eduardocasino/kim-1/3dmodels/C_Axial_L17.0mm_D6.5mm_P38.10mm_Horizontal.step

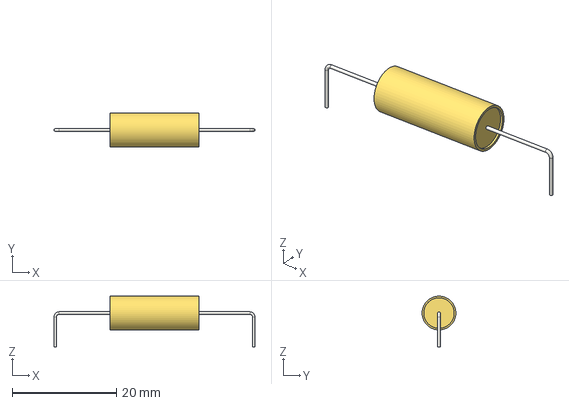
[picture p18: CAD file, 2023-03-21]
3dmodels/C_Axial_L17.0mm_D6.5mm_P38.10mm_Horizontal.step
38.6 x 6.49 x 9.75 mm
190bb9c4-b13a-11ed-bc6f-67ea0efcc404_part
190bb9c5-b13a-11ed-bc6f-67ea0efcc404_part
