eduardocasino/kim-1/3dmodels/C_Disc_D9.0mm_W2.5mm_P13.00mm.step

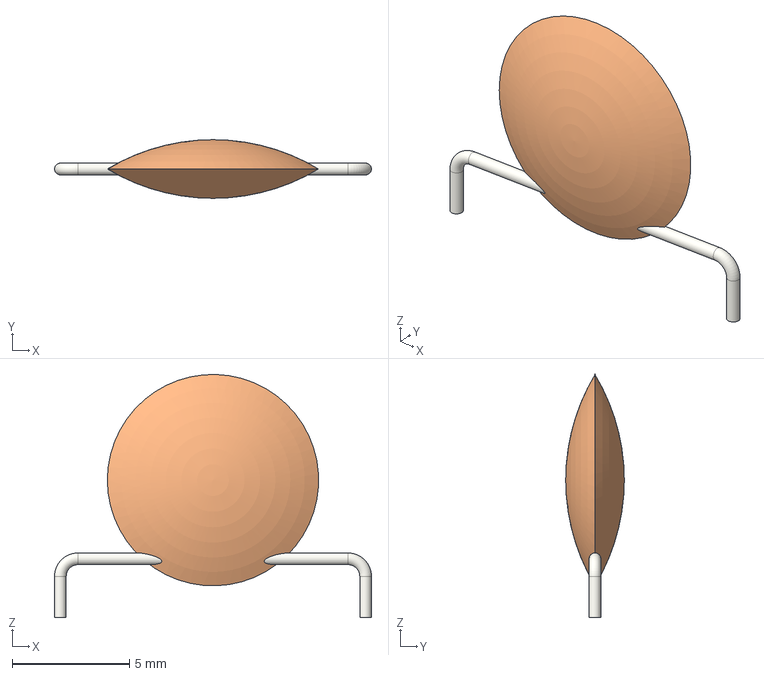
[picture p19: CAD file, 2023-03-21]
3dmodels/C_Disc_D9.0mm_W2.5mm_P13.00mm.step
13.5 x 2.50 x 10.3 mm
190bb9d0-b13a-11ed-bc6f-67ea0efcc404_part
190bb9d1-b13a-11ed-bc6f-67ea0efcc404_part
