eduardocasino/kim-1/3dmodels/C_Axial_L12.0mm_D4.5mm_P22.86mm_Horizontal.step

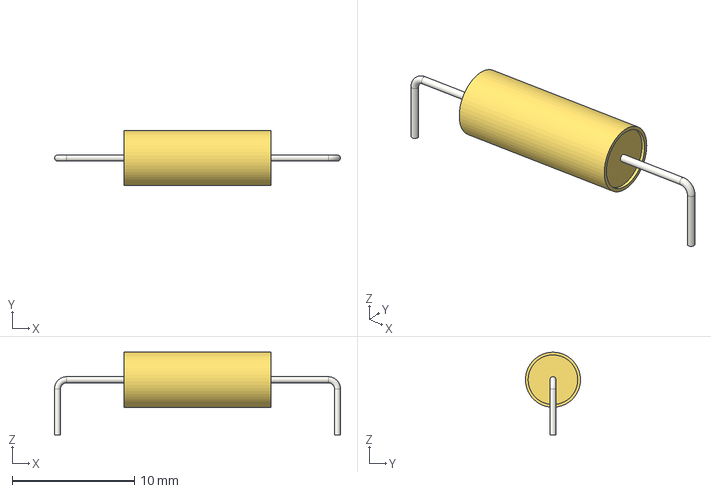
[picture p20: CAD file, 2023-03-21]
3dmodels/C_Axial_L12.0mm_D4.5mm_P22.86mm_Horizontal.step
23.4 x 4.50 x 6.75 mm
0d44160d-c6fe-11ed-94c9-bdfa26a9df0a_part
0d44160e-c6fe-11ed-94c9-bdfa26a9df0a_part
