eduardocasino/kim-1/3dmodels/res-1_4w-150R-18_0mm-Resistor-1_4w-220ohm.step

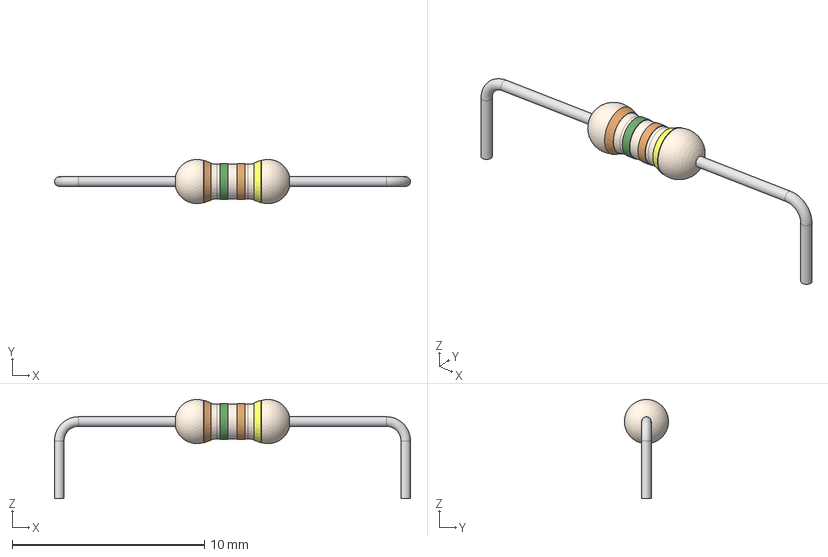
[picture p21: CAD file, 2023-03-21]
3dmodels/res-1_4w-150R-18_0mm-Resistor-1_4w-220ohm.step
18.5 x 2.29 x 5.14 mm
Resistor-body
Ring-1
Ring-2
Ring-3
Ring-4
pins
