eduardocasino/kim-1/kim-1.kicad_sch

## KiCad design kim-1.kicad_sch (2023-03-21)

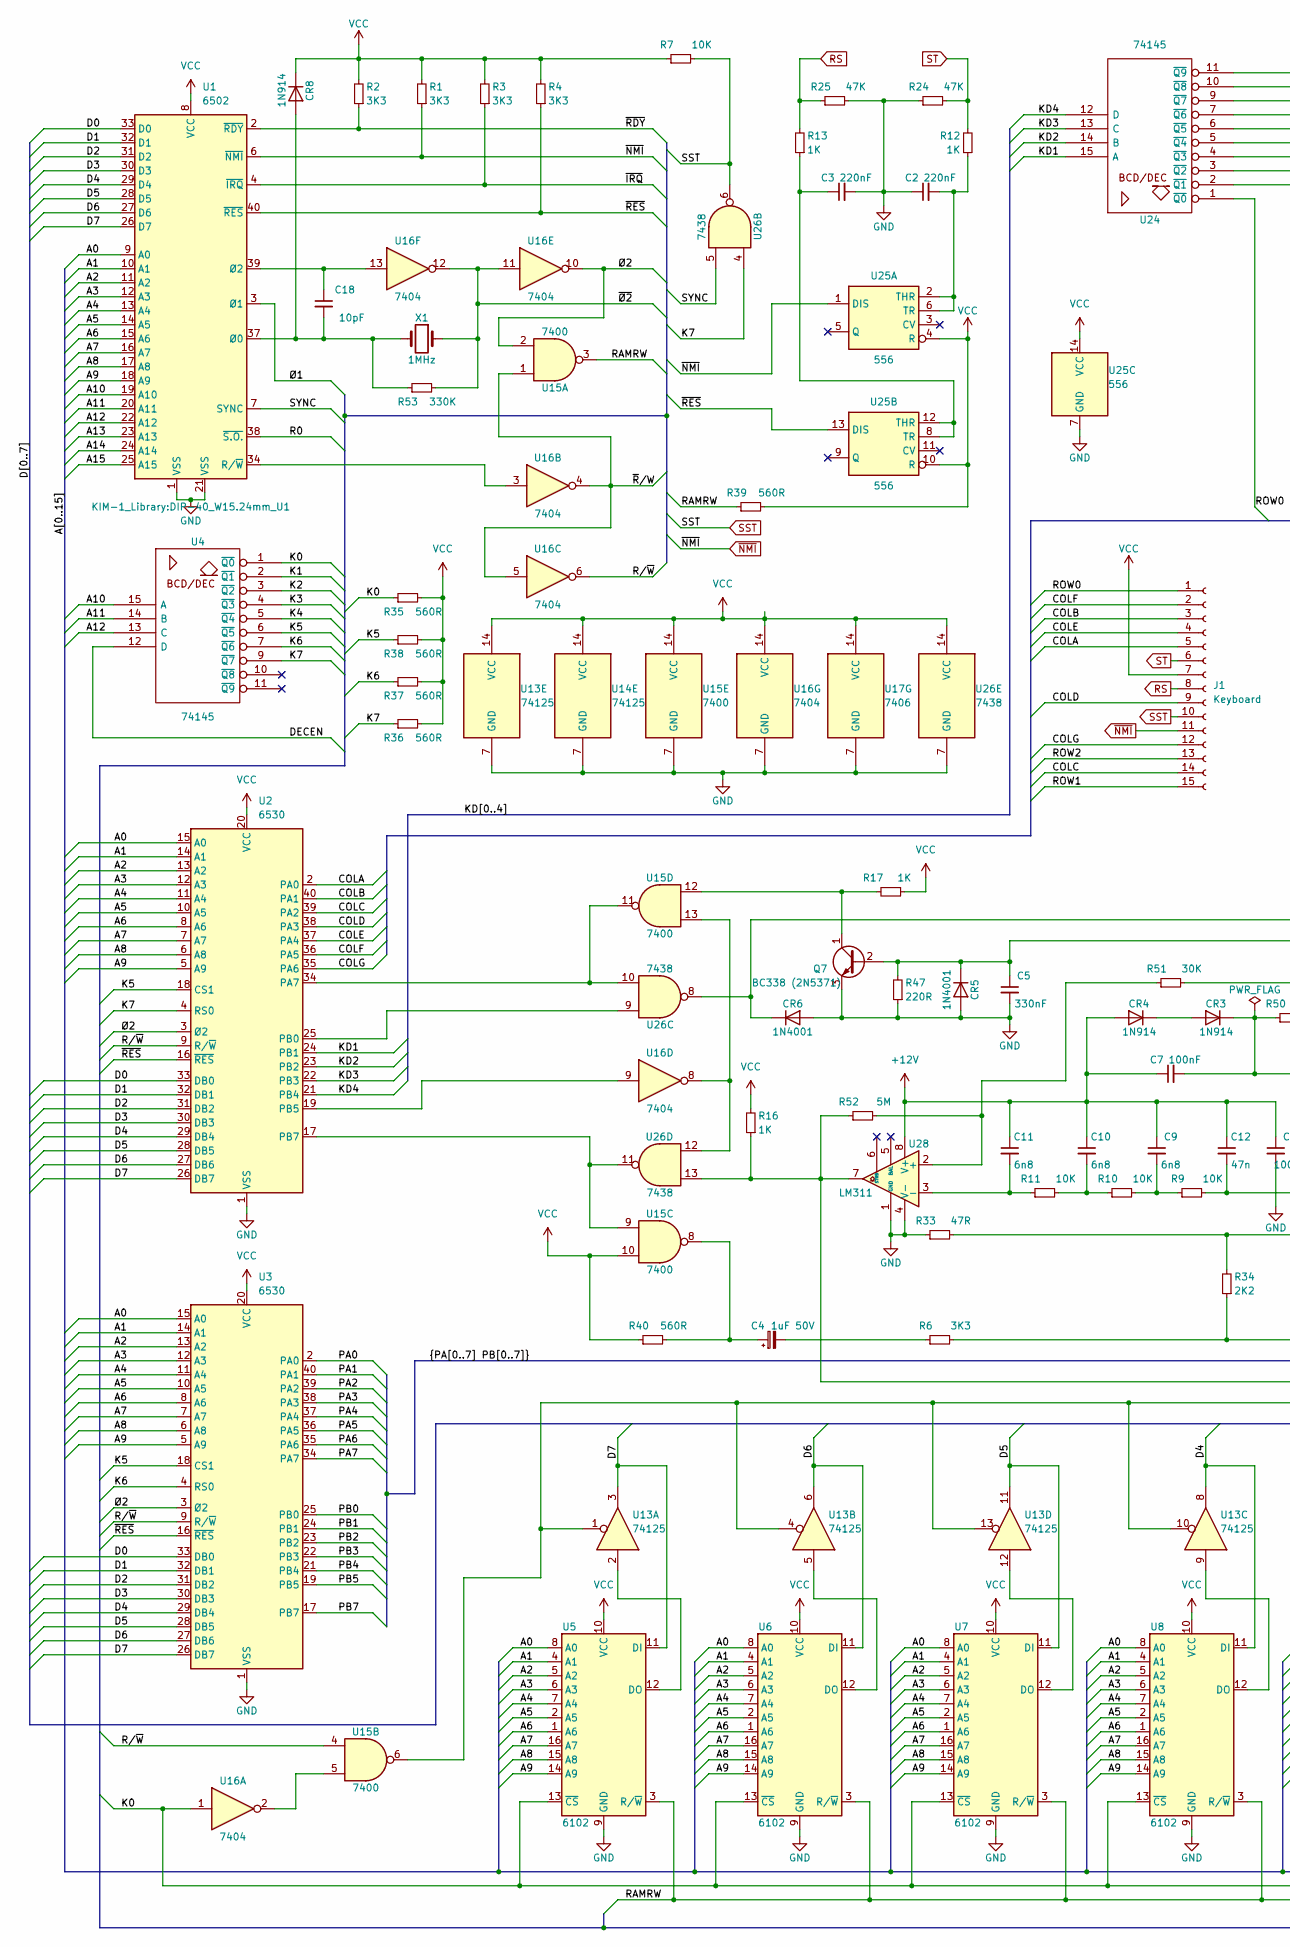
[picture p23: schematic kim-1.kicad_sch, part in row 1, column 1]

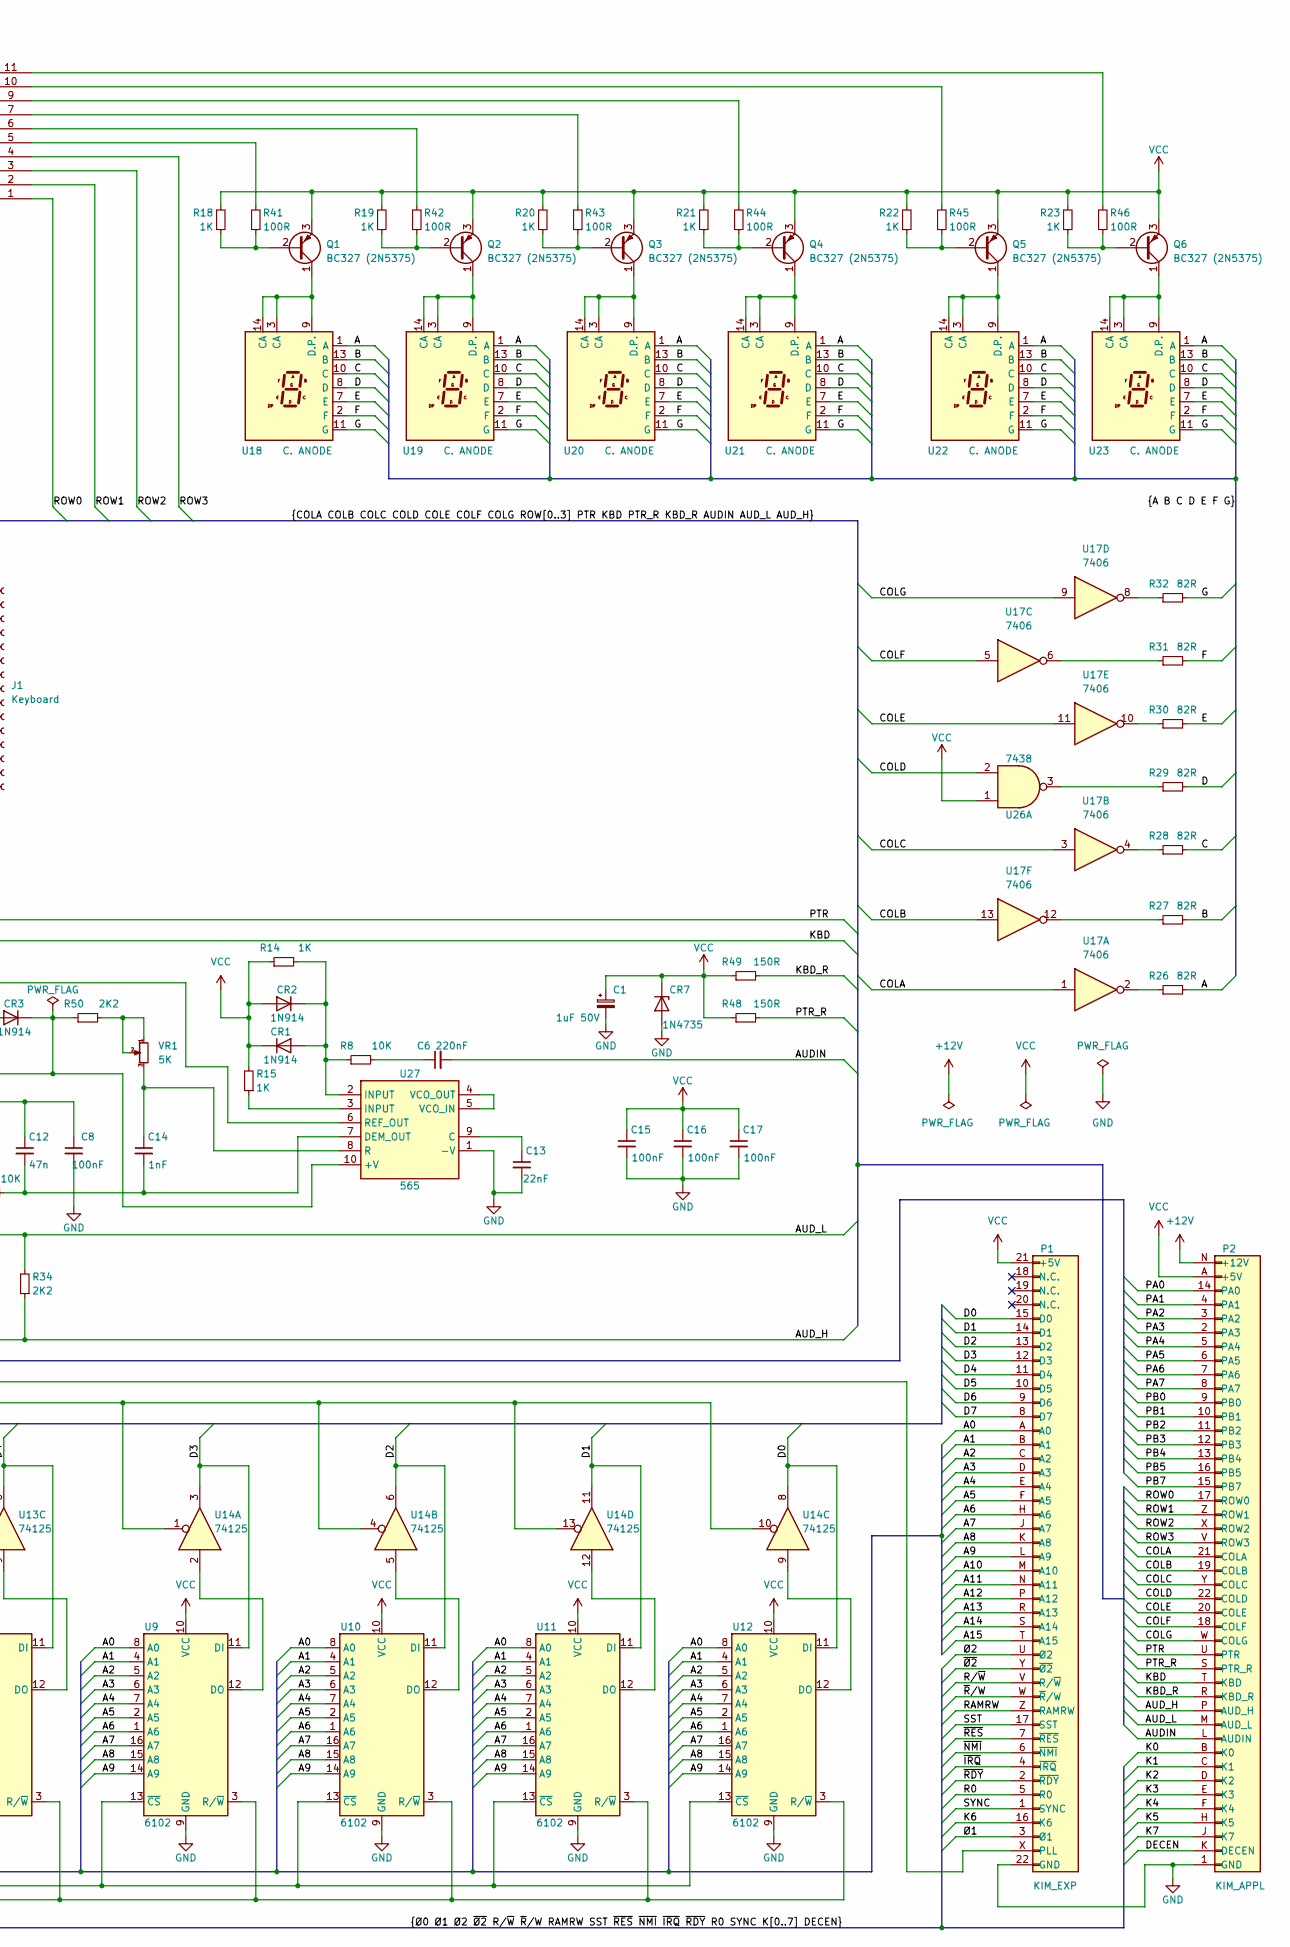
[picture p24: schematic kim-1.kicad_sch, part in row 1, column 2]

Parts:
C1, C4: 1uF 50V; CP_Axial_L11.0mm_D5.0mm_P22.86mm_Horizontal
C2, C3, C6: 220nF; C_Axial_L17.0mm_D6.5mm_P38.10mm_Horizontal
C5: 330nF; C_Axial_L17.0mm_D6.5mm_P43.18mm_Horizontal
C7, C8, C15, C16, C17: 100nF; C_Axial_L17.0mm_D6.5mm_P35.56mm_Horizontal
C9, C10, C11: 6n8; C_Axial_L12.0mm_D4.5mm_P22.86mm_Horizontal
C12: 47n; C_Axial_L12.0mm_D5.0mm_P30.48mm_Horizontal
C13: 22nF; C_Axial_L12.0mm_D5.0mm_P30.48mm_Horizontal
C14: 1nF; C_Axial_L12.0mm_D4.5mm_P22.86mm_Horizontal
C18: 10pF; C_Disc_D9.0mm_W2.5mm_P13.00mm
CR1, CR2, CR3, CR4, CR8: 1N914; D_DO-35_SOD27_P12.70mm_Horizontal
CR5, CR6: 1N4001; D_DO-41_SOD81_P12.70mm_Horizontal
CR7: 1N4735; D_DO-41_SOD81_P12.30mm_Horizontal
J1: Keyboard; PinSocket_1x15_P2.54mm_Vertical
P1: KIM_EXP; KIM_CONN
P2: KIM_APPL; KIM_CONN
Q1, Q2, Q3, Q4, Q5, Q6: BC327 (2N5375); TO-92
Q7: BC338 (2N5371); TO-92
R1, R2, R3: 3K3; R_Axial_DIN0207_3K3_L6.3mm_D2.3mm_P13mm_Horizontal
R4, R6: 3K3; R_Axial_DIN0309_3K3_L6.3mm_D2.3mm_P12.70mm_Horizontal
R7, R8, R9, R10, R11: 10K; R_Axial_DIN0309_10K_L6.3mm_D2.3mm_P12.70mm_Horizontal
R12, R13, R14, R15, R16, R17, R18, R19, R20, R21, R22, R23: 1K; R_Axial_DIN0309_1K_L6.3mm_D2.3mm_P12.70mm_Horizontal
R24, R25: 47K; R_Axial_DIN0309_47K_L6.3mm_D2.3mm_P12.70mm_Horizontal
R26, R27, R28, R29, R30, R31, R32: 82R; R_Axial_DIN0309_82R_L6.3mm_D2.3mm_P12.70mm_Horizontal
R33: 47R; R_Axial_DIN0309_47R_L6.3mm_D2.3mm_P12.70mm_Horizontal
R34, R50: 2K2; R_Axial_DIN0309_2K2_L6.3mm_D2.3mm_P12.70mm_Horizontal
R35, R36, R37, R38, R40: 560R; R_Axial_DIN0309_560R_L6.3mm_D2.3mm_P12.70mm_Horizontal
R39: 560R; R_Axial_DIN0309_560R_L6.3mm_D2.3mm_P8.70mm_Horizontal
R41, R42, R43, R44, R45, R46: 100R; R_Axial_DIN0309_100R_L6.3mm_D2.5mm_P12.70mm_Horizontal
R47: 220R; R_Axial_DIN0309_220R_L6.3mm_D2.3mm_P12.70mm_Horizontal
R48, R49: 150R; R_Axial_DIN0309_150R_L9.0mm_D3.2mm_P18.00mm_Horizontal
R51: 30K; R_Axial_DIN0309_30K_L6.3mm_D2.3mm_P12.70mm_Horizontal
R52: 5M; R_Axial_DIN0309_5M_L6.3mm_D2.3mm_P12.70mm_Horizontal
R53: 330K; R_Axial_DIN0207_330K_L6.3mm_D2.3mm_P13mm_Horizontal
U1: 6502; DIP-40_W15.24mm_U1
U2: 6530; DIP-40_W15.24mm_U2
U3: 6530; DIP-40_W15.24mm_U3
U4: 74145; DIP-16_W7.62mm
U5, U6, U7, U8, U9, U10, U11: 6102; DIP-16_W7.62mm_U5-U11
U12: 6102; DIP-16_W7.62mm_U12
U13, U14: 74125; DIP-14_W7.62mm
U15: 7400; DIP-14_W7.62mm
U16: 7404; DIP-14_W7.62mm
U17: 7406; DIP-14_W7.62mm_U17
U18: C. ANODE; MAN72A_U18
U19, U20: C. ANODE; MAN72A_U19-U20
U21: C. ANODE; MAN72A_U21
U22: C. ANODE; MAN72A_U22
U23: C. ANODE; MAN72A_U23
U24: 74145; DIP-16_W7.62mm_U24
U25: 556; DIP-14_W7.62mm
U26: 7438; DIP-14_W7.62mm
U27: 565; DIP-14_W7.62mm
U28: LM311; DIP-8_W7.62mm
VR1: 5K; Piher-PT-15-LV18
X1: 1MHz; Crystal_HC33-U_Horizontal

Connections:
+12V: C7.1, C8.1, C9.1, C10.1, C11.1, C12.1, CR4.2 (A), P2.N (+12V), U28.8 (V+)
A: R26.2, U18.1 (A), U19.1 (A), U20.1 (A), U21.1 (A), U22.1 (A), U23.1 (A)
A0: P1.A (A0), U1.9 (A0), U2.15 (A0), U3.15 (A0), U5.8 (A0), U6.8 (A0), U7.8 (A0), U8.8 (A0), U9.8 (A0), U10.8 (A0), U11.8 (A0), U12.8 (A0)
A1: P1.B (A1), U1.10 (A1), U2.14 (A1), U3.14 (A1), U5.4 (A1), U6.4 (A1), U7.4 (A1), U8.4 (A1), U9.4 (A1), U10.4 (A1), U11.4 (A1), U12.4 (A1)
A2: P1.C (A2), U1.11 (A2), U2.13 (A2), U3.13 (A2), U5.5 (A2), U6.5 (A2), U7.5 (A2), U8.5 (A2), U9.5 (A2), U10.5 (A2), U11.5 (A2), U12.5 (A2)
A3: P1.D (A3), U1.12 (A3), U2.12 (A3), U3.12 (A3), U5.6 (A3), U6.6 (A3), U7.6 (A3), U8.6 (A3), U9.6 (A3), U10.6 (A3), U11.6 (A3), U12.6 (A3)
A4: P1.E (A4), U1.13 (A4), U2.11 (A4), U3.11 (A4), U5.7 (A4), U6.7 (A4), U7.7 (A4), U8.7 (A4), U9.7 (A4), U10.7 (A4), U11.7 (A4), U12.7 (A4)
A5: P1.F (A5), U1.14 (A5), U2.10 (A5), U3.10 (A5), U5.2 (A5), U6.2 (A5), U7.2 (A5), U8.2 (A5), U9.2 (A5), U10.2 (A5), U11.2 (A5), U12.2 (A5)
A6: P1.H (A6), U1.15 (A6), U2.8 (A6), U3.8 (A6), U5.1 (A6), U6.1 (A6), U7.1 (A6), U8.1 (A6), U9.1 (A6), U10.1 (A6), U11.1 (A6), U12.1 (A6)
A7: P1.J (A7), U1.16 (A7), U2.7 (A7), U3.7 (A7), U5.16 (A7), U6.16 (A7), U7.16 (A7), U8.16 (A7), U9.16 (A7), U10.16 (A7), U11.16 (A7), U12.16 (A7)
A8: P1.K (A8), U1.17 (A8), U2.6 (A8), U3.6 (A8), U5.15 (A8), U6.15 (A8), U7.15 (A8), U8.15 (A8), U9.15 (A8), U10.15 (A8), U11.15 (A8), U12.15 (A8)
A9: P1.L (A9), U1.18 (A9), U2.5 (A9), U3.5 (A9), U5.14 (A9), U6.14 (A9), U7.14 (A9), U8.14 (A9), U9.14 (A9), U10.14 (A9), U11.14 (A9), U12.14 (A9)
A10: P1.M (A10), U1.19 (A10), U4.15 (A)
A11: P1.N (A11), U1.20 (A11), U4.14 (B)
A12: P1.P (A12), U1.22 (A12), U4.13 (C)
A13: P1.R (A13), U1.23 (A13)
A14: P1.S (A14), U1.24 (A14)
A15: P1.T (A15), U1.25 (A15)
AUDIN: C6.2, P2.L (AUDIN)
AUD_H: P2.P (AUD_H), R6.2, R34.1
AUD_L: P2.M (AUD_L), R33.2, R34.2
B: R27.2, U18.13 (B), U19.13 (B), U20.13 (B), U21.13 (B), U22.13 (B), U23.13 (B)
C: R28.2, U18.10 (C), U19.10 (C), U20.10 (C), U21.10 (C), U22.10 (C), U23.10 (C)
COLA: J1.5, P2.21 (COLA), U2.2 (PA0), U17.1
COLB: J1.3, P2.19 (COLB), U2.40 (PA1), U17.13
COLC: J1.14, P2.Y (COLC), U2.39 (PA2), U17.3
COLD: J1.9, P2.22 (COLD), U2.38 (PA3), U26.2
COLE: J1.4, P2.20 (COLE), U2.37 (PA4), U17.11
COLF: J1.2, P2.18 (COLF), U2.36 (PA5), U17.5
COLG: J1.12, P2.W (COLG), U2.35 (PA6), U17.9
D: R29.2, U18.8 (D), U19.8 (D), U20.8 (D), U21.8 (D), U22.8 (D), U23.8 (D)
D0: P1.15 (D0), U1.33 (D0), U2.33 (DB0), U3.33 (DB0), U12.11 (DI), U14.8
D1: P1.14 (D1), U1.32 (D1), U2.32 (DB1), U3.32 (DB1), U11.11 (DI), U14.11
D2: P1.13 (D2), U1.31 (D2), U2.31 (DB2), U3.31 (DB2), U10.11 (DI), U14.6
D3: P1.12 (D3), U1.30 (D3), U2.30 (DB3), U3.30 (DB3), U9.11 (DI), U14.3
D4: P1.11 (D4), U1.29 (D4), U2.29 (DB4), U3.29 (DB4), U8.11 (DI), U13.8
D5: P1.10 (D5), U1.28 (D5), U2.28 (DB5), U3.28 (DB5), U7.11 (DI), U13.11
D6: P1.9 (D6), U1.27 (D6), U2.27 (DB6), U3.27 (DB6), U6.11 (DI), U13.6
D7: P1.8 (D7), U1.26 (D7), U2.26 (DB7), U3.26 (DB7), U5.11 (DI), U13.3
DECEN: P2.K (DECEN), U4.12 (D)
E: R30.2, U18.7 (E), U19.7 (E), U20.7 (E), U21.7 (E), U22.7 (E), U23.7 (E)
F: R31.2, U18.2 (F), U19.2 (F), U20.2 (F), U21.2 (F), U22.2 (F), U23.2 (F)
G: R32.2, U18.11 (G), U19.11 (G), U20.11 (G), U21.11 (G), U22.11 (G), U23.11 (G)
GND: C1.2, C2.1, C3.2, C5.2, C8.2, C13.2, C15.2, C16.2, C17.2, CR5.2 (A), CR6.2 (A), CR7.2 (A), P1.22 (GND), P2.1 (GND), Q7.3 (E), R24.1, R25.2, R33.1, R47.1, U1.1 (VSS), U1.21 (VSS), U2.1 (VSS), U3.1 (VSS), U5.9 (GND), U6.9 (GND), U7.9 (GND), U8.9 (GND), U9.9 (GND), U10.9 (GND), U11.9 (GND), U12.9 (GND), U13.7 (GND), U14.7 (GND), U15.7 (GND), U16.7 (GND), U17.7 (GND), U25.7 (GND), U26.7 (GND), U27.1 (-V), U28.1 (GND), U28.4 (V-)
K0: P2.B (K0), R35.1, U4.1 (~Q0), U5.13 (~CS), U6.13 (~CS), U7.13 (~CS), U8.13 (~CS), U9.13 (~CS), U10.13 (~CS), U11.13 (~CS), U12.13 (~CS), U16.1
K1: P2.C (K1), U4.2 (~Q1)
K2: P2.D (K2), U4.3 (~Q2)
K3: P2.E (K3), U4.4 (~Q3)
K4: P2.F (K4), U4.5 (~Q4)
K5: P2.H (K5), R38.1, U2.18 (CS1), U3.18 (CS1), U4.6 (~Q5)
K6: P1.16 (K6), R37.1, U3.4 (RS0), U4.7 (~Q6)
K7: P2.J (K7), R36.1, U2.4 (RS0), U4.9 (~Q7), U26.4
KBD: C5.1, CR5.1 (K), P2.T (KBD), Q7.2 (B), R47.2
KBD_R: P2.R (KBD_R), R49.2
KD1: U2.24 (PB1), U24.15 (A)
KD2: U2.23 (PB2), U24.14 (B)
KD3: U2.22 (PB3), U24.13 (C)
KD4: U2.21 (PB4), U24.12 (D)
unnamed: C2.2, R12.1, U25.2 (THR), U25.6 (TR)
unnamed: C3.1, R13.1, U25.8 (TR), U25.12 (THR)
unnamed: C4.1, R40.2, U15.8
unnamed: C4.2, R6.1
unnamed: C6.1, R8.2
unnamed: C7.2, CR3.1 (K), R50.1, U27.10 (+V)
unnamed: C9.2, R9.1, R10.2
unnamed: C10.2, R10.1, R11.2
unnamed: C11.2, R11.1, U28.3 (-)
unnamed: C12.2, C14.2, R9.2, U27.7 (DEM_OUT)
unnamed: C13.1, U27.9 (C)
unnamed: C14.1, U27.8 (R), VR1.3
unnamed: C18.1, U1.39 (Ø2), U16.13
unnamed: C18.2, CR8.2 (A), R53.1, U1.37 (Ø0), X1.2
unnamed: CR1.2 (A), CR2.1 (K), R8.1, R14.2, U27.2 (INPUT)
unnamed: CR3.2 (A), CR4.1 (K)
unnamed: P1.X (PLL), R16.1, R52.1, U26.13, U28.7
unnamed: Q1.1 (C), U18.3 (CA), U18.9 (D.P.), U18.14 (CA)
unnamed: Q1.2 (B), R18.1, R41.1
unnamed: Q2.1 (C), U19.3 (CA), U19.9 (D.P.), U19.14 (CA)
unnamed: Q2.2 (B), R19.1, R42.1
unnamed: Q3.1 (C), U20.3 (CA), U20.9 (D.P.), U20.14 (CA)
unnamed: Q3.2 (B), R20.1, R43.1
unnamed: Q4.1 (C), U21.3 (CA), U21.9 (D.P.), U21.14 (CA)
unnamed: Q4.2 (B), R21.1, R44.1
unnamed: Q5.1 (C), U22.3 (CA), U22.9 (D.P.), U22.14 (CA)
unnamed: Q5.2 (B), R22.1, R45.1
unnamed: Q6.1 (C), U23.3 (CA), U23.9 (D.P.), U23.14 (CA)
unnamed: Q6.2 (B), R23.1, R46.1
unnamed: Q7.1 (C), R17.2, U15.12
unnamed: R15.1, U27.3 (INPUT)
unnamed: R26.1, U17.2
unnamed: R27.1, U17.12
unnamed: R28.1, U17.4
unnamed: R29.1, U26.3
unnamed: R30.1, U17.10
unnamed: R31.1, U17.6
unnamed: R32.1, U17.8
unnamed: R41.2, U24.5 (~Q4)
unnamed: R42.2, U24.6 (~Q5)
unnamed: R43.2, U24.7 (~Q6)
unnamed: R44.2, U24.9 (~Q7)
unnamed: R45.2, U24.10 (~Q8)
unnamed: R46.2, U24.11 (~Q9)
unnamed: R50.2, VR1.1, VR1.2
unnamed: R51.1, R52.2, U28.2 (+)
unnamed: R51.2, U27.6 (REF_OUT)
unnamed: U1.34 (R/~W), U16.3
unnamed: U2.25 (PB0), U26.9
unnamed: U10.12 (DO), U14.5
unnamed: U11.12 (DO), U14.12
unnamed: U12.12 (DO), U14.9
unnamed: U13.1, U13.4, U13.10, U13.13, U14.1, U14.4, U14.10, U14.13, U15.6
unnamed: U5.12 (DO), U13.2
unnamed: U6.12 (DO), U13.5
unnamed: U8.12 (DO), U13.9
unnamed: U7.12 (DO), U13.12
unnamed: U9.12 (DO), U14.2
unnamed: U15.5, U16.2
unnamed: U2.17 (PB7), U15.9, U26.11
unnamed: U2.34 (PA7), U15.11, U26.10
unnamed: U15.13, U16.8, U26.12
unnamed: U2.19 (PB5), U16.9
unnamed: U27.4 (VCO_OUT), U27.5 (VCO_IN)
PA0: P2.14 (PA0), U3.2 (PA0)
PA1: P2.4 (PA1), U3.40 (PA1)
PA2: P2.3 (PA2), U3.39 (PA2)
PA3: P2.2 (PA3), U3.38 (PA3)
PA4: P2.5 (PA4), U3.37 (PA4)
PA5: P2.6 (PA5), U3.36 (PA5)
PA6: P2.7 (PA6), U3.35 (PA6)
PA7: P2.8 (PA7), U3.34 (PA7)
PB0: P2.9 (PB0), U3.25 (PB0)
PB1: P2.10 (PB1), U3.24 (PB1)
PB2: P2.11 (PB2), U3.23 (PB2)
PB3: P2.12 (PB3), U3.22 (PB3)
PB4: P2.13 (PB4), U3.21 (PB4)
PB5: P2.16 (PB5), U3.19 (PB5)
PB7: P2.15 (PB7), U3.17 (PB7)
PTR: CR6.1 (K), P2.U (PTR), U26.8
PTR_R: P2.S (PTR_R), R48.2
R0: P1.5 (R0), U1.38 (~S.O.)
RAMRW: P1.Z (RAMRW), R39.1, U5.3 (R/~W), U6.3 (R/~W), U7.3 (R/~W), U8.3 (R/~W), U9.3 (R/~W), U10.3 (R/~W), U11.3 (R/~W), U12.3 (R/~W), U15.3
ROW0: J1.1, P2.17 (ROW0), U24.1 (~Q0)
ROW1: J1.15, P2.Z (ROW1), U24.2 (~Q1)
ROW2: J1.13, P2.X (ROW2), U24.3 (~Q2)
ROW3: P2.V (ROW3), U24.4 (~Q3)
RS: J1.8, R13.2, R25.1
R/~W: P1.V (R/~W), U2.9 (R/~W), U3.9 (R/~W), U15.4, U16.6
SST: J1.10, P1.17 (SST), R7.2, U26.6
ST: J1.6, R12.2, R24.2
SYNC: P1.1 (SYNC), U1.7 (SYNC), U26.5
VCC: C1.1, C15.1, C16.1, C17.1, CR1.1 (K), CR2.2 (A), CR7.1 (K), CR8.1 (K), J1.7, P1.21 (+5V), P2.A (+5V), Q1.3 (E), Q2.3 (E), Q3.3 (E), Q4.3 (E), Q5.3 (E), Q6.3 (E), R1.2, R2.2, R3.2, R4.2, R7.1, R14.1, R15.2, R16.2, R17.1, R18.2, R19.2, R20.2, R21.2, R22.2, R23.2, R35.2, R36.2, R37.2, R38.2, R39.2, R40.1, R48.1, R49.1, U1.8 (VCC), U2.20 (VCC), U3.20 (VCC), U5.10 (VCC), U6.10 (VCC), U7.10 (VCC), U8.10 (VCC), U9.10 (VCC), U10.10 (VCC), U11.10 (VCC), U12.10 (VCC), U13.14 (VCC), U14.14 (VCC), U15.10, U15.14 (VCC), U16.14 (VCC), U17.14 (VCC), U25.4 (R), U25.10 (R), U25.14 (VCC), U26.1, U26.14 (VCC)
~IRQ: P1.4 (~IRQ), R3.1, U1.4 (~IRQ)
~NMI: J1.11, P1.6 (~NMI), R1.1, U1.6 (~NMI), U25.1 (DIS)
~RDY: P1.2 (~RDY), R2.1, U1.2 (~RDY)
~RES: P1.7 (~RES), R4.1, U1.40 (~RES), U2.16 (~RES), U3.16 (~RES), U25.13 (DIS)
~R/W: P1.W (~R/W), U15.1, U16.4, U16.5
~Ø2: P1.Y (~Ø2), R53.2, U16.11, U16.12, X1.1
Ø1: P1.3 (Ø1), U1.3 (Ø1)
Ø2: P1.U (Ø2), U2.3 (Ø2), U3.3 (Ø2), U15.2, U16.10
